MarSik/hf-sampling-trx/spice/BPF-7Mhz.asc

C1: cap; 180p; ""
C2: cap; 560p; ""
C3: cap; 270p; ""
C4: cap; 560p; ""
C5: cap; 180p; ""
L1: ind; 3µ3; ""
L2: ind; 3µ3; ""
L3: ind; 3µ3; ""
R1: res; 50; ""
RLoad: res; 50; ""
V1: voltage; AC 1.; Rser=0
Named nets: 0
.ac oct 10000 100k 100Meg
HF/50MHz Receiving and Transmitting Band Pass Filters with 3 Equal Inductors 
by Tasa YU1LM
