MarSik/hf-sampling-trx/spice/classe-lnet.asc

C1: cap; 328.554pF
C2: cap; 422.193pF
C3: cap; 710.361pF
C4: cap; 27p
C5: cap; 150p
C6: cap; 390p
C7: cap; 220p
C8: cap; 390p
C9: cap; 150p
C10: cap; 27p
L1: ind; 16.2395µH
L2: ind; 1.62395µH
L3: ind; 511nH
L4: ind; 2µ2
L5: ind; 2µ2
L6: ind; 2µ2
M1: nmos; 2N7002
RGen: res; 10
RLoad: res; 50
Vbattery: voltage; 13.8; ""
Vgen: voltage; PULSE(0 12 0 25n 25n 46n 142n); ""
Named nets: 0
.tran 0 30.37u 27.94u 709.2p startup
Drawn by 'ClassE - www.TonneSoftware.com'
L total = 2.13495uH
.include irl540ns.spi
