MarSik/hf-sampling-trx/spice/classe-plain-10Mhz-tuned.asc

C1: cap; 1.285n
C2: cap; 1.402n
L1: ind; 6µH
L2: ind; 230.77nH
RLoad: res; 2.5
S1: sw; MySwitch
Vbattery: voltage; 12
Vgen: voltage; PULSE(0 12 0 5n 5n 45n 100n); Rser=0 Cpar=0
Named nets: 0
.tran 0 24.5u 22.5u 714.3p startup
.model MySwitch SW(Ron=0.080 Roff=1e6 Vt=3.5 Vh=0)
Class E amp, Vin=12V, Pout=19A, F=10Mhz
