MarSik/hf-sampling-trx/spice/classe-plain-14Mhz-tuned.asc

C1: cap; 910p
C2: cap; 1n
L1: ind; 5µH
L2: ind; 165n
RLoad: res; 2.5
S1: sw; MySwitch
Vbattery: voltage; 12
Vgen: voltage; PULSE(0 12 0 5n 5n 30.7143n 71.4286n); Rser=0 Cpar=0
Named nets: 0
.tran 0 24.5u 22.5u 714.3p startup
.model MySwitch SW(Ron=0.080 Roff=1e6 Vt=3.5 Vh=0)
Class E amp, Vin=12V, Pout=19A, F=14Mhz
