MarSik/hf-sampling-trx/spice/classe-pushpull-10Mhz-tuned-bpf.asc

C1: cap; 640p; Rser=0.015
C2: cap; 500p; Rser=25m
C3: cap; 500p; Rser=25m
C4: cap; 27p; Rser=15m
C5: cap; 150p; Rser=15m
C6: cap; 390p; Rser=15m
C7: cap; 220p; Rser=15m
C8: cap; 390p; Rser=15m
C9: cap; 150p; Rser=15m
C10: cap; 27p; Rser=15m
C11: cap; 100n; Rser=25m
C12: cap; 100n; Rser=25m
L1: ind; 20µH; Rser=0.5
L2: ind2; 55nH; Rser=0.045
L3: ind2; 55nH; Rser=0.045
L4: ind2; 110nH; Rser=0.05
L5: ind; 2µ2
L6: ind; 2µ2
L7: ind; 2µ2
RLoad: res; 50
S1: sw; MySwitch
S2: sw; MySwitch
Vbattery: voltage; 12; ""
Vgen1: voltage; PULSE(0 12 0n 0n 0n 50n 100n); ""; Rser=0.08 Cpar=0
Vgen2: voltage; PULSE(0 12 50n 0n 0n 50n 100n); ""; Rser=0.08 Cpar=0
Named nets: 0
.tran 0 24.5u 22.5u 714.3p startup
.model MySwitch SW(Ron=0.15 Roff=1e6 Vt=3.5 Vh=0)
Class E amp, Vin=12V, Pout=10W, F=10Mhz
K1 L2 L3 L4 0.99
