MarSik/hf-sampling-trx/spice/classe-pushpull-10Mhz-tuned.asc

C1: cap; 640p
C2: cap; 500p
C3: cap; 500p
L1: ind; 20µH; Rser=0.5
L2: ind2; 55nH; Rser=0.045
L3: ind2; 55nH; Rser=0.045
L4: ind2; 110nH; Rser=0.05
RLoad: res; 50
S1: sw; MySwitch
S2: sw; MySwitch
Vbattery: voltage; 12
Vgen1: voltage; PULSE(0 12 0 3n 3n 47n 100n); Rser=1 Cpar=0
Vgen2: voltage; PULSE(12 0 0 3n 3n 47n 100n); Rser=1 Cpar=0
Named nets: 0
.tran 0 24.5u 22.5u 714.3p startup
.model MySwitch SW(Ron=0.15 Roff=1e6 Vt=3.5 Vh=0)
Class E amp, Vin=12V, Pout=19A, F=10Mhz
K1 L2 L3 L4 0.99
