MarSik/hf-sampling-trx/spice/mosfet-driver-opamp.asc

C1: cap; 180p
U1: mosfet_driver
U2: LT1713
V1: voltage; 12V; Rser=0
V2: voltage; PULSE(0 3.3 0 5n 5n 45n 100n)
V3: voltage; 1.65V; ""
Named nets: 0, OUT, DRV_IN, IN
.include ZXGD3003E6.txt
.tran 0 10u 0 100p
.include TI.txt
