MarSik/hf-sampling-trx/spice/mosfet-driver.asc

C1: cap; 180p
M1: nmos; 2N7002
R1: res; 50
U1: mosfet_driver
V1: voltage; 12V; Rser=0
V2: voltage; PULSE(0 3.3 0 5n 5n 45n 100n)
Named nets: 0, OUT, DRV_IN, IN
.include ZXGD3003E6.txt
.tran 0 10u 0 100p
