MarSik/hf-sampling-trx/spice/QSD-differential.asc

C1: cap; {filterc}
C2: cap; {filterc}
C3: cap; {filterc}
C4: cap; {filterc}
C5: cap; 100n
L1: ind2; {primary}
L2: ind2; {primary}
L3: ind2; {primary}
R1: res; 50
R2: res; {opampr}
R3: res; {opampr}
R4: res; {opampr}
R5: res; {opampr}
R6: res; 200
S1: sw; QSDSW
S2: sw; QSDSW
S3: sw; QSDSW
S4: sw; QSDSW
S5: sw; QSDSW
S6: sw; QSDSW
S7: sw; QSDSW
S8: sw; QSDSW
V1: voltage; PULSE(0 5 0 1p 1p {period/4} {period})
V2: voltage; PULSE(0 5 {period/4} 1p 1p {period/4} {period})
V3: voltage; PULSE(0 5 {period/2} 1p 1p {period/4} {period})
V4: voltage; PULSE(0 5 {3*period/4} 1p 1p {period/4} {period})
V5: voltage; 2.5V
Vrf: voltage; SINE(0 2u 10000300); Rser=0
Named nets: 0, Iplus, Iminus, Qplus, Qminus, RF, bias
K1 L1 L2 L3 0.999
.param period = {1/lofreq}
.param lofreq = {10000000}
.param filterc = {220n}
.model QSDSW SW (Ron=1m Roff=1Meg Vt=2)
.param primary = {20u}
.tran 0 300m 0
.param opampr = {6e6}
